nurdagulocal66-collab/RESEARCH/Simulation/LTspice.asc

C1: cap; 22n
C8: cap; 470ľF
C9: cap; 100nF
C10: polcap; 10ľF
C11: polcap; 10ľF
C16: cap; 22n
C17: polcap; 10n; V=35
C18: polcap; 0.01ľ; V=35
C19: cap; 0.47ľ; V=35
C20: cap; 0.022; V=35
C21: cap; 100n; V=100
C22: polcap; 22ľ; V=35
C23: polcap; 100ľ; V=100
D1: schottky; MBRS360
L5: ind; 20ľ; Rser=1m
L6: ind; 20ľ; Rser=1m
L7: ind; 20ľ; Rser=1m
L8: ind; 27ľ; Rser=1m
M1: nmos; IRFH5406
M2: nmos; IRFH5406
M3: nmos; IRFH5406
M4: nmos; IRFH5406
M5: nmos; IRFH5406
M6: nmos; IRFH5406
R1: res; 1k
R2: res; 1k
R3: res; 29k
R4: res; 110
R5: res; 29k
R9: res; 0.1
R10: res; 0.1
R11: res; 0.1
R12: res; 100
R13: res; 100
R14: res; 100
R15: res; 100
R16: res; 100
R17: res; 100
R18: res; 0.01
R19: res; 0.01
R28: res; 1k
R29: res; 1k
R30: res; 29k
R31: res; 29k
R32: res; 21k
R33: res; 49.9k
R34: res; 88.7k
R35: res; 10k
U1: LT1117-3.3
U2: MCP6021
U10: MCP6021
U11: LM5576
V1: voltage; 12V
V2: voltage; 3.3V
V3: voltage; 48v
V4: voltage; PULSE(0 34 0 100n 100n 20u 40u)
V5: voltage; PULSE(0 10 21u 100n 100n 18u 40u)
V6: voltage; PULSE(0 34 13.33u 100n 100n 20u 40u)
V7: voltage; PULSE(0 10 34.33u 100n 100n 18u 40u)
V8: voltage; PULSE(0 34 26.66u 100n 100n 20u 40u)
V9: voltage; PULSE(0 10  7.66u 100n 100n 18u 40u)
V10: voltage; +1.65V
V14: voltage; 3.3V
V15: voltage; +1.65V
V16: voltage; 48V
Named nets: 0, VOUT, Ia-, Ia+, Ib-, Ib+, IA_OUT, IB_OUT
.tran 40m
